windnerd-labs/Windnerd-Core/examples/01-factory-v1/01-factory-v1.ino

/*
 * Copyright (c) 2025, windnerd.net
 * All rights reserved.
 *
 * This source code is licensed under the BSD 3-Clause License found in the
 * LICENSE file in the root directory of this source tree.
 */

#include "Arduino.h"
#include "Windnerd_Core.h"
#include "stm32g0xx_hal.h" // necessary to change clock settings

#define TIME_BEFORE_LOW_POWER (10UL * 60UL * 1000UL)


WN_Core Anemometer;

HardwareSerial SerialOutput(USART2); // TX2 on WindNerd Core board (yellow wire)
HardwareSerial SerialDebug(USART1);  // RX1 and TX1 on WindNerd Core board (headers connector)

// called every 3 seconds, gives instant wind speed + direction
void instantWindCallback(wn_instant_wind_sample_t sample)
{
  SerialOutput.print("WNI,");
  SerialOutput.print(sample.speed, 1);
  SerialOutput.print(",");
  SerialOutput.println(sample.dir);
}

// called at interval defined by setReportingIntervalInSec(), gives wind average, min and max over period defined by setAveragingPeriodInSec()
void windReportCallback(wn_wind_report_t report)
{
  SerialOutput.print("WNA,");
  SerialOutput.print(report.avg_speed, 1);
  SerialOutput.print(",");
  SerialOutput.print(report.avg_dir);
  SerialOutput.print(",");
  SerialOutput.print(report.min_speed, 1);
  SerialOutput.print(",");
  SerialOutput.println(report.max_speed, 1);
}

void setup()
{

  SerialOutput.begin(9600);
  SerialDebug.begin(115200);

  // set 10 minutes as averaging period
  if (!Anemometer.setAveragingPeriodInSec(600))
  {
    SerialDebug.print("Incorrect averaging period value");
  }

  // set 1 minute as reporting interval
  if (!Anemometer.setReportingIntervalInSec(60))
  {
    SerialDebug.print("Incorrect reporting interval value");
  }

  Anemometer.invertVanePolarity(false);                 // change to true if you notice north and south are inverted
  Anemometer.setSpeedUnit(UNIT_KPH);                    // UNIT_MS, UNIT_KN, UNIT_KPH or UNIT_MPH
  Anemometer.onInstantWindUpdate(&instantWindCallback); // set the callback for instant wind
  Anemometer.onNewWindReport(&windReportCallback);      // set the callback for average wind

  Anemometer.begin();
}

void loop()
{
  Anemometer.loop();

  // 10 minutes after start-up we switch to low power mode|
  // on board diagnostic LEDs are not active anymore but power consumption is reduced from 0.9mA to 0.6mA
  if (!Anemometer.isLowPowerMode() && millis() > TIME_BEFORE_LOW_POWER)
  {
    SerialDebug.println("Switch to low power mode");
    Anemometer.enableLowPowerMode();
  }

  // put the MCU to sleep, the WindNerd Core library uses a timer interrupt to wake it up automatically when needed
  HAL_PWR_EnterSLEEPMode(PWR_LOWPOWERREGULATOR_ON, PWR_STOPENTRY_WFI);
}

// this is an override to set the SYS clock at 8MHz in order to reduce power consumption
// this code was generated by STM32CubeMx
void SystemClock_Config(void)
{
  RCC_OscInitTypeDef RCC_OscInitStruct = {0};
  RCC_ClkInitTypeDef RCC_ClkInitStruct = {0};

  /** Configure the main internal regulator output voltage
   */
  HAL_PWREx_ControlVoltageScaling(PWR_REGULATOR_VOLTAGE_SCALE1);

  /** Initializes the RCC Oscillators according to the specified parameters
   * in the RCC_OscInitTypeDef structure.
   */
  RCC_OscInitStruct.OscillatorType = RCC_OSCILLATORTYPE_HSI;
  RCC_OscInitStruct.HSIState = RCC_HSI_ON;
  RCC_OscInitStruct.HSIDiv = RCC_HSI_DIV2;
  RCC_OscInitStruct.HSICalibrationValue = RCC_HSICALIBRATION_DEFAULT;
  RCC_OscInitStruct.PLL.PLLState = RCC_PLL_NONE;
  if (HAL_RCC_OscConfig(&RCC_OscInitStruct) != HAL_OK)
  {
    Error_Handler();
  }

  /** Initializes the CPU, AHB and APB buses clocks
   */
  RCC_ClkInitStruct.ClockType = RCC_CLOCKTYPE_HCLK | RCC_CLOCKTYPE_SYSCLK | RCC_CLOCKTYPE_PCLK1;
  RCC_ClkInitStruct.SYSCLKSource = RCC_SYSCLKSOURCE_HSI;
  RCC_ClkInitStruct.AHBCLKDivider = RCC_SYSCLK_DIV1;
  RCC_ClkInitStruct.APB1CLKDivider = RCC_HCLK_DIV1;

  if (HAL_RCC_ClockConfig(&RCC_ClkInitStruct, FLASH_LATENCY_0) != HAL_OK)
  {
    Error_Handler();
  }

  SystemCoreClockUpdate();
}
